paulrbarnard/West-Huntspill-Railway/Face Plate Artwork/1x/Train0.png

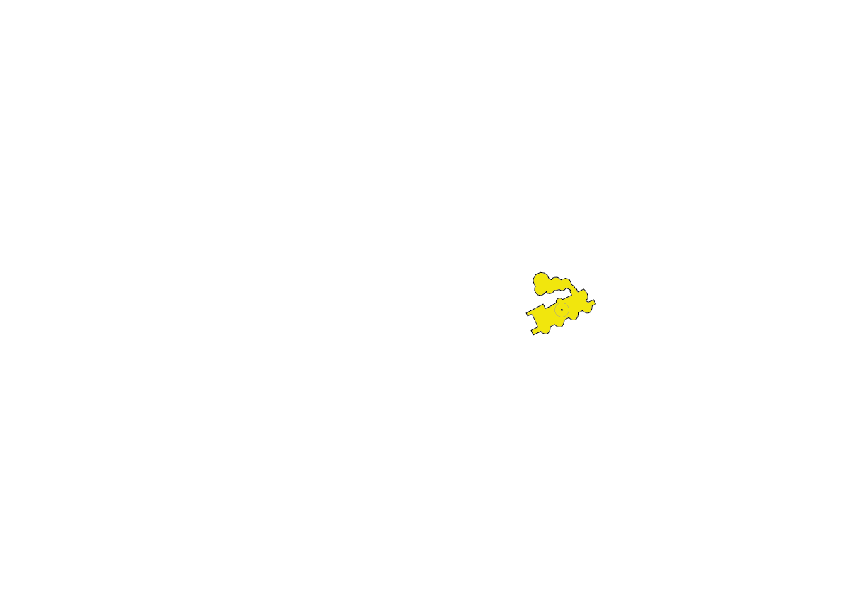
Face Plate Artwork/1x/Train0.png
