paulrbarnard/West-Huntspill-Railway/Face Plate Artwork/1x/Train1.png

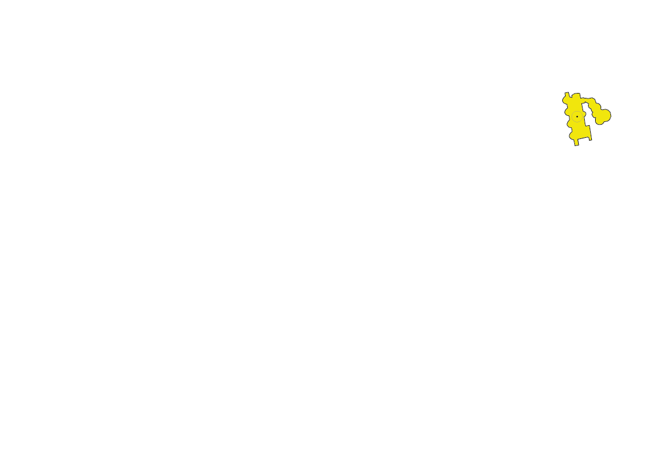
Face Plate Artwork/1x/Train1.png
