paulrbarnard/West-Huntspill-Railway/Face Plate Artwork/1x/Train5.png

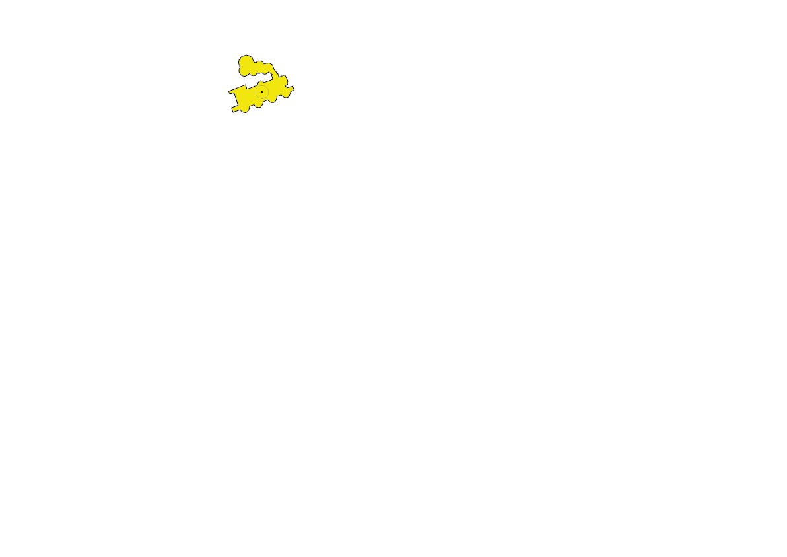
Face Plate Artwork/1x/Train5.png
