paulrbarnard/West-Huntspill-Railway/Face Plate Artwork/368w/background.png

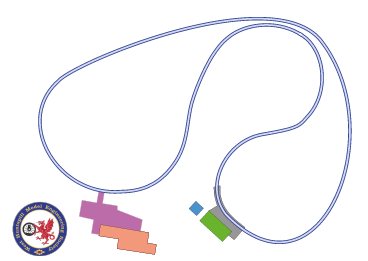
Face Plate Artwork/368w/background.png
