paulrbarnard/West-Huntspill-Railway/Face Plate Artwork/Settings Image green.png

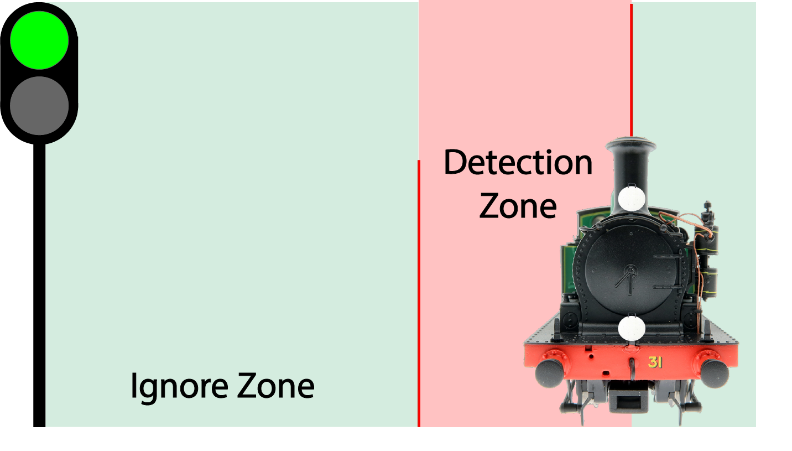
Face Plate Artwork/Settings Image green.png
